MacMannes/XVA1-User-Interface/Software/XVA1UserInterface/src/SectionFactory.h

//
// Created by André Mathlener on 16/04/2021.
//

#ifndef XVA1USERINTERFACE_SECTIONFACTORY_H
#define XVA1USERINTERFACE_SECTIONFACTORY_H

#include "Section.h"

class SectionFactory {
public:
    Section createDefaultSection();

    Section createVoiceSection();

    Section createMixerSection();

    Section createEffectsSection();

    Section createArpSection();

    Section createOscillatorSection();

    Section createEnvelopeSection();

    Section createLFOSection();

    Section createFilterSection();

    Section createPatchSection();

    Section createExternalControlsSection();

    Section createPerformanceControlsSection();

    Section createSequencerSection();
};

#endif  // XVA1USERINTERFACE_SECTIONFACTORY_H
